415labs/CampSandals/3D Rendering/LW backpacking camp shoes-sz9-render1.jpg

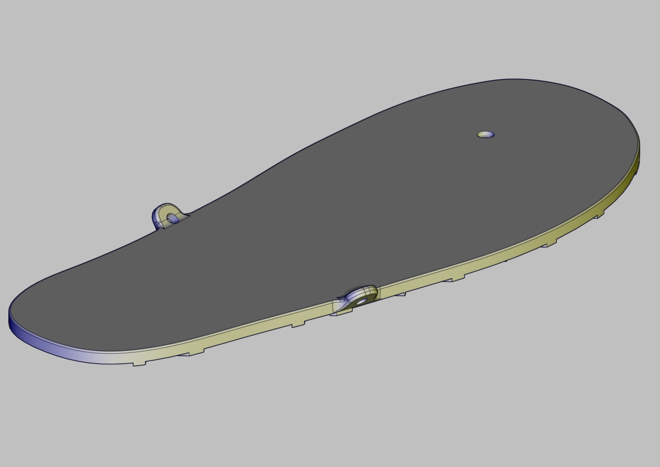
3D Rendering/LW backpacking camp shoes-sz9-render1.jpg
