415labs/CampSandals/3D Rendering/LW backpacking camp shoes-sz9-render2.jpg

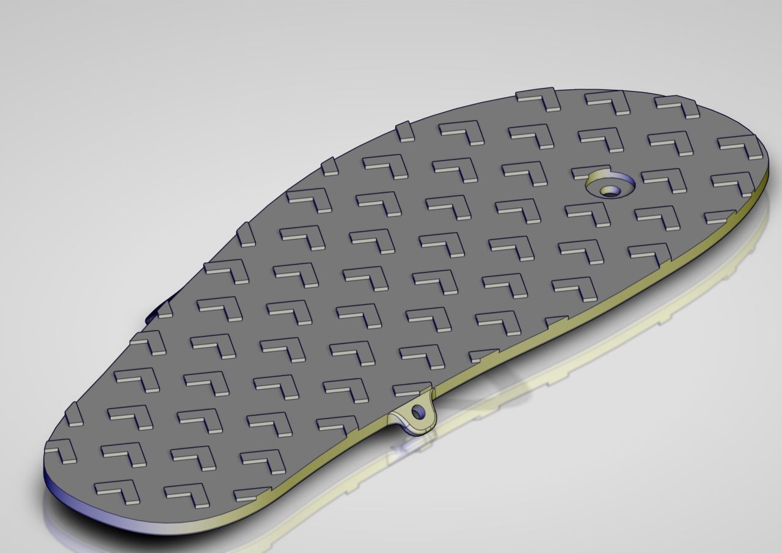
3D Rendering/LW backpacking camp shoes-sz9-render2.jpg
