415labs/CampSandals/3D Rendering/LW backpacking camp shoes-sz9-render3.jpg

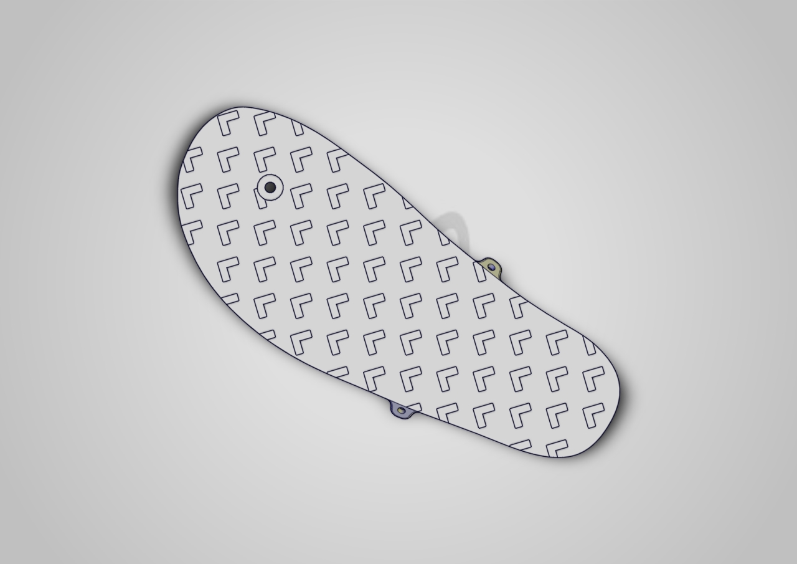
3D Rendering/LW backpacking camp shoes-sz9-render3.jpg
