415labs/CampSandals/3D Rendering/LW backpacking camp shoes-sz9.png

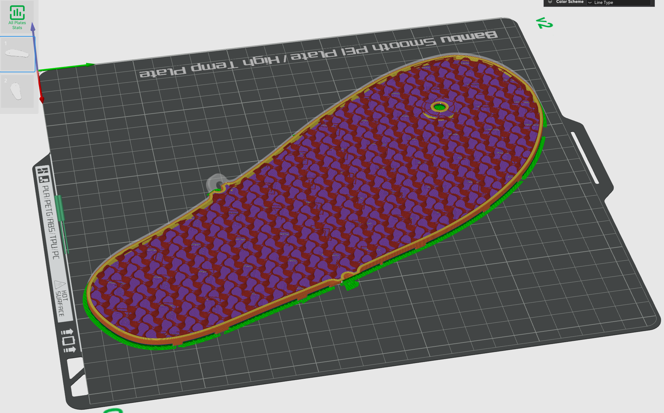
3D Rendering/LW backpacking camp shoes-sz9.png
