415labs/CampSandals/Photos/415Labs-Lightweight backpacking camp shoes-photo7.jpg

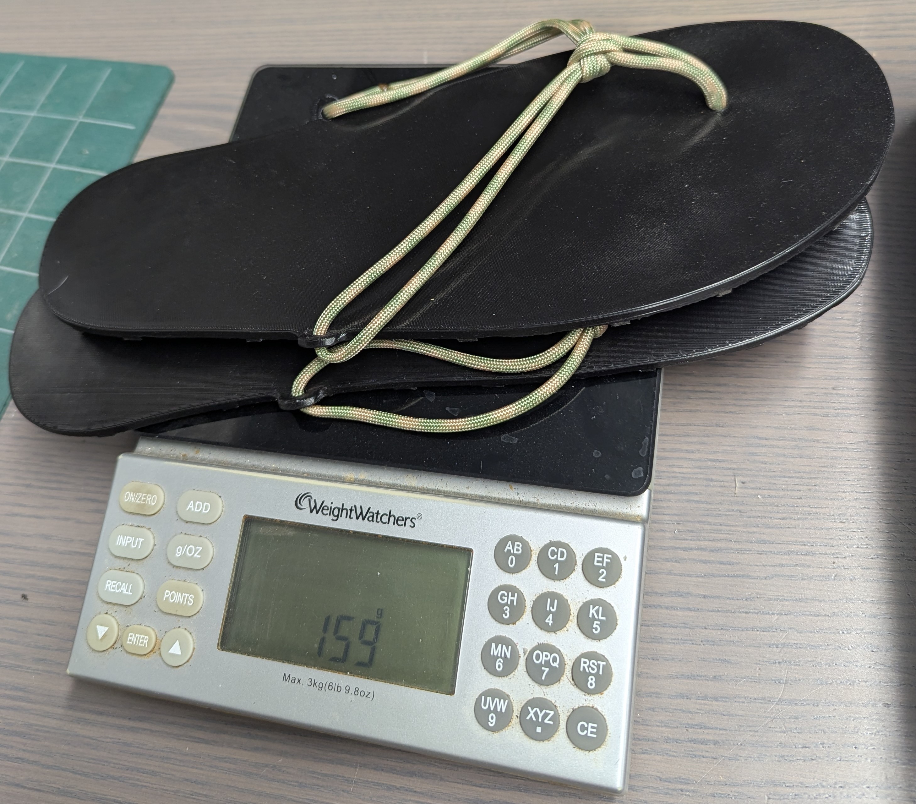
Photos/415Labs-Lightweight backpacking camp shoes-photo7.jpg
